timmhayes/lifeline-reminder/src/LVGL_Driver.h

#pragma once

#include <lvgl.h>
#include <lv_conf.h>
#include "Display_ST7789.h"

#define LVGL_WIDTH    (LCD_WIDTH )
#define LVGL_HEIGHT   LCD_HEIGHT
#define LVGL_BUF_LEN  (LVGL_WIDTH * LVGL_HEIGHT / 20)

#define EXAMPLE_LVGL_TICK_PERIOD_MS  5


void Lvgl_Display_LCD( lv_disp_drv_t *disp_drv, const lv_area_t *area, lv_color_t *color_p );
void Lvgl_Touchpad_Read( lv_indev_drv_t * indev_drv, lv_indev_data_t * data );
void example_increase_lvgl_tick(void *arg);

void Lvgl_Init(void);
